koolcat6666/Engine-Simulator-2.0/firmware/wheel_defs.h

/* vim: set syntax=c expandtab sw=2 softtabstop=2 autoindent smartindent smarttab : */
/*
 * Arbritrary wheel pattern generator wheel definitions
 *
 * copyright 2014 David J. Andruczyk
 * 
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
 */
  #ifndef __WHEEL_DEFS_H__
  #define __WHEEL_DEFS_H__
   #ifdef ESP32
   #include <pgmspace.h>
   #else
   #include <avr/pgmspace.h>
   #endif

  /* Struttura che descrive una ruota fonica.
   * - decoder_name      : nome descrittivo della ruota
   * - edge_states_ptr   : puntatore all'array degli stati di edge (Crank/Cam1/Cam2)
   * - wheel_rpm_scaling : fattore di scalatura RPM (num_edges/120 per ruote crank)
   * - wheel_max_edges   : numero di edge nell'array (usato dalla ISR)
   * - wheel_degrees     : gradi totali di rotazione (360 crank, 720 con cam)
   */
  typedef struct {
    const char *decoder_name;
    const byte *edge_states_ptr;
    float wheel_rpm_scaling;
    uint16_t wheel_max_edges;
    uint16_t wheel_degrees;
  } wheels;
  
 /* Wheel patterns! 
  *
  * Wheel patterns define the pin states and specific times. The ISR runs 
  * at a constant speed related to the requested RPM. The request RPM is 
  * scaled based on the LENGTH of each wheel's array.  The reference is 
  * the 60-2 which was the first decoder designed which has 120 "edges" 
  * (transitions" for each revolution of the wheel. Any other wheel that 
  * also has 120 edges has and RPM scaling factor of 1.0. IF a wheel has 
  * less edges needed to "describe" it, it's number of edges are divided by 120 to
  * get the scaling factor which is applied to the RPM calculation.
  * There is an enumeration (below) that lists the defined wheel types, 
  * as well as an array listing the rpm_scaling factors with regards to 
  * each pattern.
  * 
  * NOTE: There is MORE THAN ONE WAY to define a wheel pattern.  You can 
  * use more edges to get to 1 deg accuracy but the side effect is that 
  * your maximum RPM is capped because of that. Currently 60-2 can run 
  * up to about 60,000 RPM, 360and8 can only do about 10,000 RPM becasue 
  * it has 6x the number of edges...  The less edges, the faster it can go... :)
  * 
  * Using more edges allows you to do things like vary the dutycycle,  
  * i.e. a simple non-missing tooth 50% duty cycle wheel can be defined 
  * with only 2 entries if you really want, but I didn't do it that way 
  * for some of the simple ones as it made it seem somewhat confusing
  * to look at as it required you to keep the rpm_scaler factor in mind.  
  * Most/all patterns show the pulses you're receive for one revolution
  * of a REAL wheel on a real engine.
  */

  /*
   * Values to use within a wheel definition. 
   * 0 means no tooth on any wheel definition
   * 1 means crank tooth
   * 2 means cam1 tooth
   * 4 means cam2 tooth
   * 
   * combinations of numbers mean all of the related teeth are present, 
   * eg  3 means crank and cam1, 5 means crank and cam2, 6 means cam1 and cam2, 7 means crank, cam1 and cam2 
   */

  
  /* Wheel types we know about...
   * This enumerations is the INDEX into the Wheels[] array of structures
   * defined in main file. That struct contains pointers to the following:
   * wheel name in a user friendly string
   * pointer to the wheel edge array used by the ISR
   * RPM scaling factor (num_edges/120 for crank wheels)
   * Number of edges in the edge array above, needed by the ISR 
   */
 typedef enum { 
   DIZZY_FOUR_CYLINDER,  /* 2 evenly spaced teeth */
   DIZZY_SIX_CYLINDER,   /* 3 evenly spaced teeth */
   DIZZY_EIGHT_CYLINDER, /* 4 evenly spaced teeth */
   SIXTY_MINUS_TWO,      /* 60-2 crank only */
   SIXTY_MINUS_TWO_WITH_CAM, /* 60-2 with 2nd trigger on cam */
   SIXTY_MINUS_TWO_WITH_HALFMOON_CAM, /* 60-2 with "half moon" trigger on cam */
   THIRTY_SIX_MINUS_ONE, /* 36-1 crank only */
   TWENTY_FOUR_MINUS_ONE,
   FOUR_MINUS_ONE_WITH_CAM, /* 4-1 crank + cam */
   EIGHT_MINUS_ONE,       /* 8-1 crank only */
   SIX_MINUS_ONE_WITH_CAM,/* 6-1 crank + cam */
   TWELVE_MINUS_ONE_WITH_CAM, /* 12-1 crank + cam */
   FOURTY_MINUS_ONE,      /* Ford V-10 40-1 crank only */
   DIZZY_FOUR_TRIGGER_RETURN,  /* dizzy 4 cylinder signal, 40deg on 50 deg off */
   ODDFIRE_VR,            /* Oddfire V-twin */
   OPTISPARK_LT1,         /* Optispark 360 and 8 */
   TWELVE_MINUS_THREE,    /* 12-3 */
   THIRTY_SIX_MINUS_TWO_TWO_TWO, /* 36-2-2-2 crank only H4 */
   THIRTY_SIX_MINUS_TWO_TWO_TWO_H6, /* 36-2-2-2 crank only H6 */
   THIRTY_SIX_MINUS_TWO_TWO_TWO_WITH_CAM, /* 36-2-2-2 crank and cam */
   FOURTY_TWO_HUNDRED_WHEEL, /* 4200 wheel */
   THIRTY_SIX_MINUS_ONE_WITH_CAM_FE3, /* Mazda F3 36-1 crank and cam */
   SIX_G_SEVENTY_TWO_WITH_CAM, /* Mitsubishi DOHC CAS and TCDS 6G72 */
   BUELL_ODDFIRE_CAM,     /* Buell 45 deg cam wheel */
   GM_LS1_CRANK_AND_CAM,  /* GM LS1 24 tooth with cam */
   GM_58x_LS_CRANK_4X_CAM, /* GM 58x LS crank 4x cam wheel */
   LOTUS_THIRTY_SIX_MINUS_ONE_ONE_ONE_ONE, /* Lotus crank wheel 36-1-1-1-1 */
   HONDA_RC51_WITH_CAM,   /* Honda oddfire 90 deg V-twin */
   THIRTY_SIX_MINUS_ONE_WITH_SECOND_TRIGGER, /* From jimstim */
   CHRYSLER_NGC_THIRTY_SIX_PLUS_TWO_MINUS_TWO_WITH_NGC4_CAM, /* Chrysler NGC 36+2-2 crank with NGC 4 cylinder cam pattern */
   CHRYSLER_NGC_THIRTY_SIX_MINUS_TWO_PLUS_TWO_WITH_NGC6_CAM, /* Chrysler NGC 36-2+2 crank with NGC 6 cylinder cam pattern */
   CHRYSLER_NGC_THIRTY_SIX_MINUS_TWO_PLUS_TWO_WITH_NGC8_CAM, /* Chrysler NGC 36-2+2 crank with NGC 8 cylinder cam pattern */
   WEBER_IAW_WITH_CAM, /* From jimstim IAW weber-marelli */
   FIAT_ONE_POINT_EIGHT_SIXTEEN_VALVE_WITH_CAM, /* Fiat 1.8 16V from jimstim */
   THREE_SIXTY_NISSAN_CAS, /*from jimstim 360 tooth cas with 6 slots */
   TWENTY_FOUR_MINUS_TWO_WITH_SECOND_TRIGGER, /* Mazda CAS 24-1 inner ring single pulse outer ring */
   YAMAHA_EIGHT_TOOTH_WITH_CAM, /* 02-03 Yamaha R1, seank */
   GM_FOUR_TOOTH_WITH_CAM, /* GM 4 even crank with half moon cam */
   GM_SIX_TOOTH_WITH_CAM, /* GM 4 even crank with half moon cam */
   GM_EIGHT_TOOTH_WITH_CAM, /* GM 4 even crank with half moon cam */
   VOLVO_D12ACD_WITH_CAM, /* Volvo Diesel d12[acd] with cam (alex32 on forums.libreems.org */
   MAZDA_THIRTY_SIX_MINUS_TWO_TWO_TWO_WITH_SIX_TOOTH_CAM,
   MITSUBISH_4g63_4_2,
   AUDI_135_WITH_CAM,
   HONDA_D17_NO_CAM,
   MAZDA_323_AU,
   DAIHATSU_3CYL,
   MIATA_9905,
   TWELVE_WITH_CAM, //12 evenly spaced crank teeth and a single cam tooth
   TWENTY_FOUR_WITH_CAM, //24 evenly spaced crank teeth and a single cam tooth
   SUBARU_SIX_SEVEN,      /* Subaru 6 crank, 7 cam */
   GM_7X,                 /* GM 7X pattern. 6 even teeth with 1 extra uneven tooth */
   FOUR_TWENTY_A,         /* DSM 420a */
   FORD_ST170,            /* Ford ST170 */
   MITSUBISHI_3A92,        /* Mitsubishi 3cylinder 3A92 */
   TOYOTA_4AGE_CAS,           /*Toyota 4AGE CAS, 4 teeth and one cam tooth*/
   TOYOTA_4AGZE,           /*Toyota 4AGZE, 24 teeth and one cam tooth*/
   SUZUKI_DRZ400,         /* Suzuki DRZ-400 6 coil "tooths", 2 uneven crank tooths */
   JEEP2000_4CYL,  /* Jeep 2.5 4cyl aka jeep2000_4cyl */
   JEEP2000_6CYL,  /* Jeep 4.0 6cyl aka jeep2000_6cyl */
   BMW_N20, //BMW N20 58x and custom cam wheels
   VIPER_96_02, // Dodge Viper 1996-2002 wheel pattern
   THIRTY_SIX_MINUS_TWO_WITH_ONE_CAM, // 36-2 with  1 tooth cam - 2jz-gte VVTI crank pulley + non-vvti cam
   GM_40_OSS, // GM 40 tooth wheel no skips for transmission OSS simulation

   MAX_WHEELS,
 }WheelType;

/* Name strings for EACH wheel type, for serial UI */
 const char dizzy_four_cylinder_friendly_name[] PROGMEM = "4 cylinder dizzy";
 const char dizzy_six_cylinder_friendly_name[] PROGMEM = "6 cylinder dizzy";
 const char dizzy_eight_cylinder_friendly_name[] PROGMEM = "8 cylinder dizzy";
 const char sixty_minus_two_friendly_name[] PROGMEM = "60-2 crank only";
 const char sixty_minus_two_with_cam_friendly_name[] PROGMEM = "60-2 crank and cam";
 const char sixty_minus_two_with_halfmoon_cam_friendly_name[] PROGMEM = "60-2 crank and 'half moon' cam";
 const char thirty_six_minus_one_friendly_name[] PROGMEM = "36-1 crank only";
 const char twenty_four_minus_one_friendly_name[] PROGMEM = "24-1 crank only";
 const char four_minus_one_with_cam_friendly_name[] PROGMEM = "4-1 crank wheel with cam";
 const char eight_minus_one_friendly_name[] PROGMEM = "8-1 crank only (R6)";
 const char six_minus_one_with_cam_friendly_name[] PROGMEM = "6-1 crank with cam";
 const char twelve_minus_one_with_cam_friendly_name[] PROGMEM = "12-1 crank with cam";
 const char fourty_minus_one_friendly_name[] PROGMEM = "40-1 crank only (Ford V10)";
 const char dizzy_four_trigger_return_friendly_name[] PROGMEM = "Distributor style 4 cyl 50deg off, 40 deg on";
 const char oddfire_vr_friendly_name[] PROGMEM = "odd fire 90 deg pattern 0 and 135 pulses";
 const char optispark_lt1_friendly_name[] PROGMEM = "GM OptiSpark LT1 360 and 8";
 const char twelve_minus_three_friendly_name[] PROGMEM = "12-3 oddball";
 const char thirty_six_minus_two_two_two_friendly_name[] PROGMEM = "36-2-2-2 H4 Crank only";
 const char thirty_six_minus_two_two_two_h6_friendly_name[] PROGMEM = "36-2-2-2 H6 Crank only";
 const char thirty_six_minus_two_two_two_with_cam_friendly_name[] PROGMEM = "36-2-2-2 Crank and cam";
 const char fourty_two_hundred_wheel_friendly_name[] PROGMEM = "GM 4200 crank wheel";
 const char thirty_six_minus_one_with_cam_fe3_friendly_name[] PROGMEM = "Mazda FE3 36-1 with cam";
 const char six_g_seventy_two_with_cam_friendly_name[] PROGMEM = "Mitsubishi 6g72 with cam";
 const char buell_oddfire_cam_friendly_name[] PROGMEM = "Buell Oddfire CAM wheel";
 const char gm_ls1_crank_and_cam_friendly_name[] PROGMEM = "GM LS1 crank and cam";
 const char gm_ls_58X_crank_and_4x_cam_friendly_name[] PROGMEM = "GM 58x crank and 4x cam";
 const char lotus_thirty_six_minus_one_one_one_one_friendly_name[] PROGMEM = "Odd Lotus 36-1-1-1-1 flywheel";
 const char honda_rc51_with_cam_friendly_name[] PROGMEM = "Honda RC51 with cam";
 const char thirty_six_minus_one_with_second_trigger_friendly_name[] PROGMEM = "36-1 crank with 2nd trigger on teeth 33-34";
 const char chrysler_ngc_thirty_six_plus_two_minus_two_with_ngc4_cam_friendly_name[] PROGMEM = "Chrysler NGC 36+2-2 crank, NGC 4-cyl cam";
 const char chrysler_ngc_thirty_six_minus_two_plus_two_with_ngc6_cam_friendly_name[] PROGMEM = "Chrysler NGC 36-2+2 crank, NGC 6-cyl cam";
 const char chrysler_ngc_thirty_six_minus_two_plus_two_with_ngc8_cam_friendly_name[] PROGMEM = "Chrysler NGC 36-2+2 crank, NGC 8-cyl cam";
 const char weber_iaw_with_cam_friendly_name[] PROGMEM = "Weber-Marelli 8 crank+2 cam pattern";
 const char fiat_one_point_eight_sixteen_valve_with_cam_friendly_name[] PROGMEM = "Fiat 1.8 16V crank and cam";
 const char three_sixty_nissan_cas_friendly_name[] PROGMEM = "Nissan 360 CAS with 6 slots";
 const char twenty_four_minus_two_with_second_trigger_friendly_name[] PROGMEM = "Mazda CAS 24-2 with single pulse outer ring";
 const char yamaha_eight_tooth_with_cam_friendly_name[] PROGMEM = "Yamaha 2002-03 R1 8 even-tooth crank with 1 tooth cam";
 const char gm_four_tooth_with_cam_friendly_name[] PROGMEM = "GM 4 even-tooth crank with 1 tooth cam";
 const char gm_six_tooth_with_cam_friendly_name[] PROGMEM = "GM 6 even-tooth crank with 1 tooth cam";
 const char gm_eight_tooth_with_cam_friendly_name[] PROGMEM = "GM 8 even-tooth crank with 1 tooth cam";
 const char volvo_d12acd_with_cam_friendly_name[] PROGMEM = "Volvo d12[acd] crank with 7 tooth cam";
 const char mazda_thirty_six_minus_two_two_two_with_six_tooth_cam_friendly_name[] PROGMEM = "Mazda 36-2-2-2 with 6 tooth cam";
 const char mitsubishi_4g63_4_2_friendly_name[] PROGMEM = "Mitsubishi 4g63 aka 4/2 crank and cam";
 const char audi_135_with_cam_friendly_name[] PROGMEM = "Audi 135 tooth crank and cam";
 const char honda_d17_no_cam_friendly_name[] PROGMEM = "Honda D17 Crank (12+1)";
 const char mazda_323_au_friendly_name[] PROGMEM = "Mazda 323 AU version";
 const char daihatsu_3cyl_friendly_name[] PROGMEM = "Daihatsu 3+1 distributor (3 cylinders)";
 const char miata_9905_friendly_name[] PROGMEM = "Miata 99-05";
 const char twelve_with_cam_friendly_name[] PROGMEM = "12/1 (12 crank with cam)";
 const char twenty_four_with_cam_friendly_name[] PROGMEM = "24/1 (24 crank with cam)";
 const char subaru_six_seven_name_friendly_name[] PROGMEM = "Subaru 6/7 crank and cam";
 const char gm_seven_x_friendly_name[] PROGMEM = "GM 7X";
 const char four_twenty_a_friendly_name[] PROGMEM = "DSM 420a";
 const char ford_st170_friendly_name[] PROGMEM = "Ford ST170";
 const char mitsubishi_3A92_friendly_name[] PROGMEM = "Mitsubishi 3A92";
 const char Toyota_4AGE_CAS_friendly_name[] PROGMEM = "Toyota 4AGE";
 const char Toyota_4AGZE_friendly_name[] PROGMEM = "Toyota 4AGZE";
 const char Suzuki_DRZ400_friendly_name[] PROGMEM = "Suzuki DRZ400";
 const char Jeep_2000_4cyl_friendly_name[] PROGMEM = "Jeep 2000 4cyl";
 const char Jeep_2000_6cyl_friendly_name[] PROGMEM = "Jeep 2000 6 cyl";
 const char BMW_N20_friendly_name[] PROGMEM = "BMW N20";
 const char VIPER9602_friendly_name[] PROGMEM = "Dodge Viper V10 1996-2002";
 const char thirty_six_minus_two_with_second_trigger_friendly_name[] PROGMEM = "36-2 with 1 tooth cam";
 const char GM_40_Tooth_Trans_OSS_friendly_name[] PROGMEM = "GM 40 tooth OSS wheel for Transmissions";

 /* Very simple 50% duty cycle */
 const unsigned char dizzy_four_cylinder[] PROGMEM = 
   { /* dizzy 4 cylinder */
     1,0,1,0 /* two pulses per crank revolution (one per cylinder) */
   };
   
 /* Very simple 50% duty cycle */
 const unsigned char dizzy_six_cylinder[] PROGMEM = 
   { /* dizzy 6 cylinder */
     1,0,1,0,1,0 /* three pulses per crank revolution (one per cylinder) */
   };
   
 /* Very simple 50% duty cycle */
 const unsigned char dizzy_eight_cylinder[] PROGMEM = 
   { /* dizzy 8 cyl */
     1,0,1,0,1,0,1,0 /* four pulses per crank revolution (one per cylinder) */
   };
   
 /* Standard bosch 60-2 pattern, 50% duty cyctle during normal teeth */
 const unsigned char sixty_minus_two[] PROGMEM = 
   { /* 60-2 */
     1,0,1,0,1,0,1,0,1,0,  /* teeth 1-5 */ 
     1,0,1,0,1,0,1,0,1,0,  /* teeth 6-10 */
     1,0,1,0,1,0,1,0,1,0,  /* teeth 11-15 */
     1,0,1,0,1,0,1,0,1,0,  /* teeth 16-20 */
     1,0,1,0,1,0,1,0,1,0,  /* teeth 21-25 */
     1,0,1,0,1,0,1,0,1,0,  /* teeth 26-30 */
     1,0,1,0,1,0,1,0,1,0,  /* teeth 31-35 */
     1,0,1,0,1,0,1,0,1,0,  /* teeth 36-40 */
     1,0,1,0,1,0,1,0,1,0,  /* teeth 41-45 */
     1,0,1,0,1,0,1,0,1,0,  /* teeth 46-50 */
     1,0,1,0,1,0,1,0,1,0,  /* teeth 51-55 */
     1,0,1,0,1,0,0,0,0,0   /* teeth 56-58 and 59-60 MISSING */
   };
 
 /* Bosch 60-2 pattern with 2nd trigger on rotation 2, 
  * 50% duty cyctle during normal teeth */
 const unsigned char sixty_minus_two_with_cam[] PROGMEM = 
   { /* 60-2 */
     1,0,1,0,1,0,1,0,1,0,  /* teeth 1-5 */ 
     1,0,1,0,1,0,1,0,1,0,  /* teeth 6-10 */
     1,0,1,0,1,0,1,0,1,0,  /* teeth 11-15 */
     1,0,1,0,1,0,1,0,1,0,  /* teeth 16-20 */
     1,0,1,0,1,0,1,0,1,0,  /* teeth 21-25 */
     1,0,1,0,1,0,1,0,1,0,  /* teeth 26-30 */
     1,0,1,0,1,0,1,0,1,0,  /* teeth 31-35 */
     1,0,1,0,1,0,1,0,1,0,  /* teeth 36-40 */
     1,0,1,0,1,0,1,0,1,0,  /* teeth 41-45 */
     1,0,1,0,1,0,1,0,1,0,  /* teeth 46-50 */
     1,0,1,0,1,0,1,0,1,0,  /* teeth 51-55 */
     1,0,1,0,1,0,0,0,0,0,  /* teeth 56-58 and 59-60 MISSING */
     1,0,1,0,1,0,1,0,1,0,  /* Second revolution teeth 1-5 */ 
     1,0,1,0,1,0,1,0,1,0,  /* teeth 6-10 */
     1,0,1,0,1,0,1,0,1,0,  /* teeth 11-15 */
     1,0,1,0,1,0,1,0,1,0,  /* teeth 16-20 */
     1,0,1,0,1,0,1,0,1,0,  /* teeth 21-25 */
     1,0,1,0,1,0,1,0,1,0,  /* teeth 26-30 */
     1,0,1,0,1,0,1,0,1,0,  /* teeth 31-35 */
     1,2,1,0,1,0,1,0,1,0,  /* teeth 36-40, Cam trigger on latter half of 36th */
     1,0,1,0,1,0,1,0,1,0,  /* teeth 41-45 */
     1,0,1,0,1,0,1,0,1,0,  /* teeth 46-50 */
     1,0,1,0,1,0,1,0,1,0,  /* teeth 51-55 */
     1,0,1,0,1,0,0,0,0,0   /* teeth 56-58 and 59-60 MISSING */
   };
 
 /* 60-2 pattern with half moon cam trigger (cam input is high for one rotation and low for second rotation),
  * 50% duty cyctle during normal teeth */
 const unsigned char sixty_minus_two_with_halfmoon_cam[] PROGMEM = 
   { /* 60-2 */
     1,0,1,0,1,0,1,0,1,0,  /* teeth 1-5 */ 
     1,0,1,0,1,0,1,0,1,0,  /* teeth 6-10 */
     1,0,1,0,1,0,1,0,1,0,  /* teeth 11-15 */
     1,0,1,0,1,0,1,0,1,0,  /* teeth 16-20 */
     1,0,1,0,1,0,1,0,1,0,  /* teeth 21-25 */
     1,0,1,0,1,0,1,0,1,0,  /* teeth 26-30 */
     1,0,1,0,1,0,1,0,1,0,  /* teeth 31-35 */
     1,0,1,0,1,0,1,0,1,0,  /* teeth 36-40 */
     1,0,1,0,1,0,3,2,3,2,  /* teeth 41-45, Cam trigger goes high on 44th tooth */
     3,2,3,2,3,2,3,2,3,2,  /* teeth 46-50 */
     3,2,3,2,3,2,3,2,3,2,  /* teeth 51-55 */
     3,2,3,2,3,2,2,2,2,2,  /* teeth 56-58 and 59-60 MISSING */
     3,2,3,2,3,2,3,2,3,2,  /* Second revolution teeth 1-5 */ 
     3,2,3,2,3,2,3,2,3,2,  /* teeth 6-10 */
     3,2,3,2,3,2,3,2,3,2,  /* teeth 11-15 */
     3,2,3,2,3,2,3,2,3,2,  /* teeth 16-20 */
     3,2,3,2,3,2,3,2,3,2,  /* teeth 21-25 */
     3,2,3,2,3,2,3,2,3,2,  /* teeth 26-30 */
     3,2,3,2,3,2,3,2,3,2,  /* teeth 31-35 */
     3,2,3,2,3,2,3,2,3,2,  /* teeth 36-40 */
     3,2,3,2,3,2,1,0,1,0,  /* teeth 41-45, Cam trigger goes low on 43th tooth on rotation 2 */
     1,0,1,0,1,0,1,0,1,0,  /* teeth 46-50 */
     1,0,1,0,1,0,1,0,1,0,  /* teeth 51-55 */
     1,0,1,0,1,0,0,0,0,0   /* teeth 56-58 and 59-60 MISSING */
   };
 
 /* Standard ford/mazda and aftermarket 36-1 pattern, 50% duty cyctle during normal teeth */  
 const unsigned char thirty_six_minus_one[] PROGMEM = 
   { /* 36-1 */
     1,0,1,0,1,0,1,0,1,0,  /* teeth 1-5 */
     1,0,1,0,1,0,1,0,1,0,  /* teeth 6-10 */
     1,0,1,0,1,0,1,0,1,0,  /* teeth 11-15 */
     1,0,1,0,1,0,1,0,1,0,  /* teeth 16-20 */
     1,0,1,0,1,0,1,0,1,0,  /* teeth 21-25 */
     1,0,1,0,1,0,1,0,1,0,  /* teeth 26-30 */
     1,0,1,0,1,0,1,0,1,0,  /* teeth 31-35 */
     0,0                   /* MISSING 36th tooth  */
   }; 
   
  /* Standard ford/mazda and aftermarket 36-1 pattern, 50% duty cyctle during normal teeth */  
 const unsigned char twenty_four_minus_one[] PROGMEM = 
   { /* 36-1 */
     1,0,1,0,1,0,  /* teeth 1-3 */
     1,0,1,0,1,0,  /* teeth 4-6 */
     1,0,1,0,1,0,  /* teeth 7-9 */
     1,0,1,0,1,0,  /* teeth 10-12 */
     1,0,1,0,1,0,  /* teeth 13-15 */
     1,0,1,0,1,0,  /* teeth 16-18 */
     1,0,1,0,1,0,  /* teeth 19-21 */
     1,0,1,0,0,0,  /* teeth 22-21 */
   }; 
   
 /* 4-1 crank signal 50% duty cycle with Cam tooth enabled during the second rotation prior to tooth 2 */
 const unsigned char four_minus_one_with_cam[] PROGMEM = 
   { /* 4-1 with cam */
     0,1,0,1,0,1,0,0,  /* Teeth 1-3, then MISSING */
     0,1,2,1,0,1,0,0   /* Tooth 5, 2nd trigger on cam between 5 and 6 
						  then 6 and 7 and MISSING 8th */
   };
   
 /* Yamaha R6 crank trigger 8 teeth missing one, (22.5deg low, 22.5deg high) 50% duty cycle during normal teeth */
 const unsigned char eight_minus_one[] PROGMEM = 
   { /* 8-1 */
     0,1,0,1,0,1,0,1,  /* Teeth 1-4 */
     0,1,0,1,0,1,0,0   /* Teeth 5-7, then MISSING */
   };
  
  /* 40deg low, 20 deg high per tooth, cam signal on second rotation during 40deg low portion of 3rd tooth */
 const unsigned char six_minus_one_with_cam[] PROGMEM = 
   { /* 6-1 with cam */
     0,0,1,0,0,1,0,0,1,  /* Teeth 1-3 */
     0,0,1,0,0,1,0,0,0,  /* Teeth 4 and 5 and MISSING 6th */
     0,0,1,0,0,1,2,2,1,  /* 2nd rev teeth 7 and 8, then 2nd trigger on cam between 8 and 9 */
     0,0,1,0,0,1,0,0,0   /* teeth 10 and 11 then missing 12th */
   };
  
  /* 25 deg low, 5 deg high, #12 is missing,  cam is high for 25 deg on second crank rotation just after tooth 21 (9) */
 const unsigned char twelve_minus_one_with_cam[] PROGMEM = 
   { /* 12-1 with cam */
     0,0,0,0,0,1,0,0,0,0,0,1, /* Teeth 1 and 2 */
     0,0,0,0,0,1,0,0,0,0,0,1, /* Teeth 3 and 4 */
	   0,0,0,0,0,1,0,0,0,0,0,1, /* Teeth 5 and 6 */
	   0,0,0,0,0,1,0,0,0,0,0,1, /* Teeth 7 and 8 */
	   0,0,0,0,0,1,0,0,0,0,0,1, /* Teeth 9 and 10 */
	   0,0,0,0,0,1,0,0,0,0,0,0, /* Tooth 11 and MISSING twelth */
     //0,0,0,0,0,1,0,0,0,0,0,1, /* Tooth 11 and WITHOUT MISSING twelth */
	   0,0,0,0,0,1,0,0,0,0,0,1, /* 2nd rotation: Teeth 13 and 14 */
	   0,0,0,0,0,1,0,0,0,0,0,1, /* Teeth 15 and 16 */
	   0,0,0,0,0,1,0,0,0,0,0,1, /* Teeth 17 and 18 */
	   0,0,0,0,0,1,0,0,0,0,0,1, /* Teeth 19 and 20 */
	   0,0,0,0,0,1,2,2,2,2,2,1, /* Tooth 21 and 22,  2nd trigger on cam between teeth 21 and 22 for 25 deg */
	   0,0,0,0,0,1,0,0,0,0,0,0  /* Totth 23 and MISSING 24th */
     //0,0,0,0,0,1,0,0,0,0,0,1  /* Totth 23 and WITHOUT MISSING 24th */
   };
   
  /* Ford V10 version of EDIS with 40 teeth instead of 36, 50% duty cycle during normal teeth.. */
 const unsigned char fourty_minus_one[] PROGMEM = 
   { /* 40-1 */
     0,1,0,1,0,1,0,1,0,1,  /* Teeth 1-5 */
     0,1,0,1,0,1,0,1,0,1,  /* Teeth 6-10 */ 
     0,1,0,1,0,1,0,1,0,1,  /* Teeth 11-15 */ 
     0,1,0,1,0,1,0,1,0,1,  /* Teeth 16-20 */ 
     0,1,0,1,0,1,0,1,0,1,  /* Teeth 21-25 */ 
     0,1,0,1,0,1,0,1,0,1,  /* Teeth 26-30 */ 
     0,1,0,1,0,1,0,1,0,1,  /* Teeth 31-35 */ 
     0,1,0,1,0,1,0,1,0,0   /* Teeth 36-39 and MISSING 40th tooth */ 
   };
  
  /* 50deg off, 40 deg on dissy style signal */
  const unsigned char dizzy_four_trigger_return[] PROGMEM = 
    { /* dizzy trigger return */
      0,0,0,0,0,1,1,1,1l  /* Simple off/on signal, 50deg off, 40 deg on */
    };
   
  /* Oddfire V twin  135/225 split */
  const unsigned char oddfire_vr[] PROGMEM = 
    { /* Oddfire VR */
      1,0,0,0,0,0,0,0,0,1,0,0, /* Tooth 1 and 2 at 0 deg and 135 deg, then 225 off */
      0,0,0,0,0,0,0,0,0,0,0,0 
    };
  
  /* GM LT1 360 and 8 wheel, see http://powerefi.com/files/opti-LT1-count.JPG */
  const unsigned char optispark_lt1[] PROGMEM = 
    { /* Optispark 360 outside teeth, 8 varying inside teeth */
    /* 1   2   3   4   5   6   7   8   9   10  11  12  13  14  15  16  17  18  19  20  21  22  23  24  25  26  27  28  29  30 */
      0,1,0,1,0,1,0,1,0,1,0,1,0,1,0,1,0,1,0,1,
      0,1,0,1,0,1,0,1,0,1,0,1,0,1,0,1,0,1,0,1,
      0,1,0,1,0,1,0,1,0,1,0,1,0,1,0,1,0,1,0,1, /* 0-30 */
      0,1,0,1,0,1,0,1,0,1,0,1,0,1,0,1,0,1,0,1,
      0,1,0,1,0,1,2,3,2,3,2,3,2,3,2,3,2,3,2,3,
      0,1,0,1,0,1,0,1,0,1,0,1,0,1,0,1,0,1,0,1, /* 31-60 */
      0,1,0,1,0,1,0,1,0,1,0,1,0,1,0,1,0,1,0,1,
      0,1,0,1,0,1,0,1,0,1,0,1,0,1,0,1,0,1,0,1,
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
		 * 55 deg high, 5 deg low, 65 deg high, 5 deg low,
		 * 45 deg high, 5 deg low, (360 degreees ) */
      1,1,1,1,1,1,1,1,1,1, 
	  1,0,1,1,1,1,1,1,1,1, 
	  1,1,1,0,1,0,1,1,1,1, 
	  1,1,1,1,1,0,1,1,1,1,
	  1,1,1,1,1,1,1,0,1,1,
	  1,1,1,1,1,1,1,1,1,1,
	  1,0,1,1,1,1,1,1,1,1,
	  1,0
  };

 /* Mazda F3 36-1 with cam */
 const unsigned char thirty_six_minus_one_with_cam_fe3[] PROGMEM = 
   { /* 36-1 with cam, 3 cam teeth, 2 180deg from each other */
     1,0,1,0,1,0,1,0,1,0,1,0, /* 0-55 deg */
     1,0,1,0,1,0,3,2,3,0,1,0, /* 60-115 deg  cam tooth at 90 deg crank for 15 crank degrees */
     1,0,1,0,1,0,1,0,1,0,1,0, /* 120-175 deg */
     1,0,1,0,1,0,1,0,1,0,1,0, /* 180-235 deg */
     1,0,1,0,1,0,1,0,1,0,1,0, /* 240-295 deg */
     1,0,1,0,1,0,1,0,1,0,0,0, /* 300-355 deg Crank missing tooth at end */
     1,0,1,0,1,0,1,0,1,0,1,0, /* 360-415 deg */
     3,2,3,0,1,0,3,2,3,0,1,0, /* 420-475 deg 2 more cam teeth at 420 and 450 deg, 15 crank degrees each */
     1,0,1,0,1,0,1,0,1,0,1,0, /* 480-535 deg */
     1,0,1,0,1,0,1,0,1,0,1,0, /* 540-595 deg */
     1,0,1,0,1,0,1,0,1,0,1,0, /* 600-655 deg */
     1,0,1,0,1,0,1,0,1,0,0,0  /* 660-715 deg Crank missing tooth at end */
   }; 
  
  /* Mitsubishi 6g72 crank/cam */
  const unsigned char six_g_seventy_two_with_cam[] PROGMEM = 
    { /* Mitsubishi 6g72 */
	  /* Crank signal's are 50 deg wide, and one per cylinder
	   * Cam signals have 3 40 deg wide teeh and one 85 deg wide tooth
	   * Counting both From TDC#1
	   * Crank: 40 deg high, 70 deg low (repeats whole cycle)
	   * Cam: 70 deg high, 80 deg low, 40 deg high, 150 deg low,
	   * 40 deg high, 130 deg low, 40 deg high, 155 deg low 
	   */
      3,3,3,3,3,3,3,3,3,2,
      2,2,2,2,0,0,0,0,0,0,
      0,0,0,1,1,1,1,1,1,1,
      3,3,3,2,2,2,2,2,0,0,
      0,0,0,0,0,0,0,1,1,1,
      1,1,1,1,1,1,1,0,0,0,
      0,0,0,0,0,0,0,0,2,2,
      2,3,3,3,3,3,1,1,1,1,
      1,0,0,0,0,0,0,0,0,0,
      0,0,0,0,0,1,1,1,1,1,
      1,1,3,3,3,2,2,2,2,2,
      0,0,0,0,0,0,0,0,0,1,
      1,1,1,1,1,1,1,1,1,0,
      0,0,0,0,0,0,0,0,0,0,
      0,2,2,3
    };
   
  const unsigned char buell_oddfire_cam[] PROGMEM = 
    { /* Buell oddfire cam wheel */
	  /* Wheel is a cam wheel (degress are in crank degrees 
	   * 36 deg high, 54 deg low,
	   * 36 deg high, 54 deg low,
	   * (Rear at TDC) 36 deg high,
	   * 1889 deg low, 36 deg high
	   * 54 deg low, 36 deg high,
	   * 54 deg low, (Front at TDC),
	   * 36 deg high, 99 deg low
	   */
	  1,1,1,1,0,0,0,0,0,0, /* Tooth 1 (36 deg) and 54 deg space */
	  1,1,1,1,0,0,0,0,0,0, /* Tooth 2 (36 deg) and 54 deg space */
	  1,1,1,1,0,0,0,0,0,0, /* Tooth 3 (36 deg) and begin of 189 deg space */
	  0,0,0,0,0,0,0,0,0,0, /* Part of 189 deg space */
	  0,0,0,0,0,1,1,1,1,0, /* Tail of 189 deg space, 36 deg tooth, begin of 54 deg space */
	  0,0,0,0,0,1,1,1,1,0, /* Tail of 54 deg space, 36 deg tooth, begin of 54 deg space */
	  0,0,0,0,0,1,1,1,1,0, /* Tail of 54 deg space, last 36 deg tooth, begin of 99 deg space */
	  0,0,0,0,0,0,0,0,0,0  /* Tail of 99 deg space */
    };
  
  const unsigned char gm_ls1_crank_and_cam[] PROGMEM = 
    { /* GM LS1 24 tooth crank snd 1 tooth cam */
	  /* 12 deg low, 3 deg high, 3 deg low,
	   * 12 deg high, 3deg low, 12 deg high,
	   * 3 deg low, 12 deg high, 3 deg low,
	   * 12 deg high, 3 deg low, 12 deg high,
	   * 12 deg low, 3 deg high, 3 deg low,
	   * 12 deg high, 3 deg low, 12 deg high,
	   * 3 deg low, 12 deg high, 12 deg low,
	   * 3 deg high, 12 deg low, 3 deg high,
	   * 3 deg low, 12 deg high, 3 deg low,
	   * 12 deg high, 12 deg low, 3 deg high,
	   * 12 deg low, 3 deg high, 12 deg low,
	   * 3 deg high, 12 deg low, 3 deg high,
	   * 3 deg low, 12 deg high, 12 deg low,
	   * 3 deg high, 3 deg low, 12 deg high,
	   * 12 deg low, 3 deg high, 12 deg low,
	   * 3 deg high, 12 deg low, 3 deg high
	   * Second rotation is the SAME pattern
	   * with cam signal held high for 360 
	   * crank degrees */
      4,0,0,0,0,0,0,0,0,0,0,0,1,1,1,0,0,0,1,1,
      1,1,1,1,1,1,1,1,1,1,0,0,0,1,1,1,1,1,1,1,
      1,1,1,1,1,0,0,0,1,1,1,1,1,1,1,1,1,1,1,1,
      0,0,0,1,1,1,1,1,1,1,1,1,1,1,1,0,0,0,1,1,
      1,1,1,1,1,1,1,1,1,1,0,0,0,0,0,0,0,0,0,0,
      0,0,1,1,1,0,0,0,1,1,1,1,1,1,1,1,1,1,1,1,
      0,0,0,1,1,1,1,1,1,1,1,1,1,1,1,0,0,0,1,1,
      1,1,1,1,1,1,1,1,1,1,0,0,0,0,0,0,0,0,0,0,
      0,0,1,1,1,0,0,0,0,0,0,0,0,0,0,0,0,1,1,1,
      0,0,0,1,1,1,1,1,1,1,1,1,1,1,1,0,0,0,1,1,
      1,1,1,1,1,1,1,1,1,1,0,0,0,0,0,0,0,0,0,0,
      0,0,1,1,1,0,0,0,0,0,0,0,0,0,0,0,0,1,1,1,
      0,0,0,0,0,0,0,0,0,0,0,0,1,1,1,0,0,0,1,1,
      1,1,1,1,1,1,1,1,1,1,0,0,0,0,0,0,0,0,0,0,
      0,0,1,1,1,0,0,0,1,1,1,1,1,1,1,1,1,1,1,1,
      0,0,0,0,0,0,0,0,0,0,0,0,1,1,1,0,0,0,0,0,
      0,0,0,0,0,0,0,1,1,1,0,0,0,0,0,0,0,0,0,0,
      0,0,1,1,1,0,0,0,0,0,0,0,0,0,0,0,0,1,1,1,
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
     1,0,1,0,1,0,1,0,1,0, /* Teeth 11-15 */
     1,0,1,0,1,0,1,0,1,0, /* Teeth 16-20 */
     1,0,1,0,1,0,1,0,1,0, /* Teeth 21-25 */
     1,0,1,0,1,0,1,0,1,0, /* Teeth 26-30 */
     1,0,1,0,1,0,1,0,0,0, /* Teeth 31-34, 35th tooth missing  */
     0,0                  /* 36th MISSING tooth */
   };

   // GM 40 tooth OSS wheel for transmission simulation. Simple on/off 40 teeth for 360* of rotation with no missing teeth.
   //Added by Dale Follett of Twisted Builds LLC 02-23-2025 for transmission controller simulation.
  const unsigned char GM40toothOSS[] PROGMEM = 
   {
      1,0,1,0,1,0,1,0,1,0, // Teeth 0-5
      1,0,1,0,1,0,1,0,1,0, // Teeth 6-10
      1,0,1,0,1,0,1,0,1,0, // Teeth 11-15
      1,0,1,0,1,0,1,0,1,0, // Teeth 16-20
      1,0,1,0,1,0,1,0,1,0, // Teeth 21-25
      1,0,1,0,1,0,1,0,1,0, // Teeth 26-30
      1,0,1,0,1,0,1,0,1,0, // Teeth 31-35
      1,0,1,0,1,0,1,0,1,0, // Teeth 36-40
   };

#endif
